Kelvysb/OpenDials/Hardware/Printing/V2/Dial/Dial-Body.stl

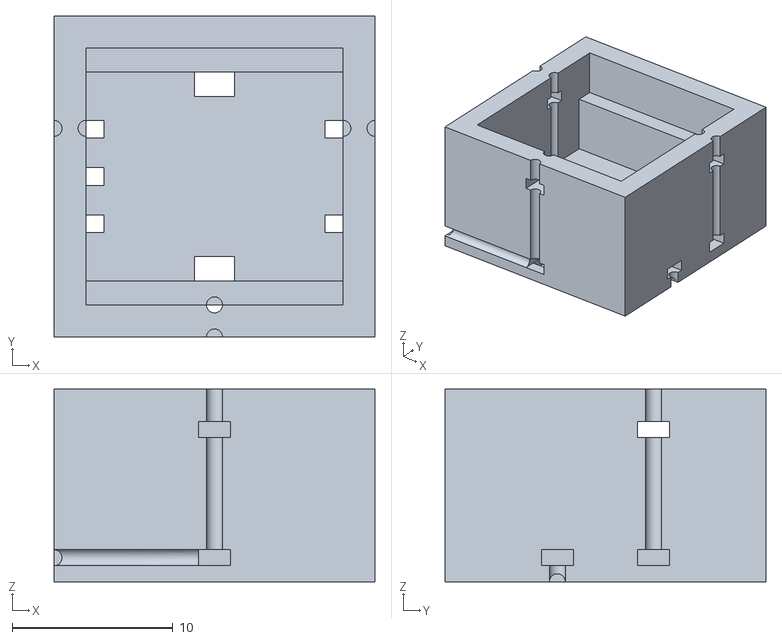
[picture p17: CAD file, 2023-11-05, an earlier design]
Hardware/Printing/V2/Dial/Dial-Body.stl
20.0 x 20.0 x 12.0
