Kelvysb/OpenDials/Hardware/Printing/V2/DPad/CE3_OpenDials_v2-DPad-Body.3mf

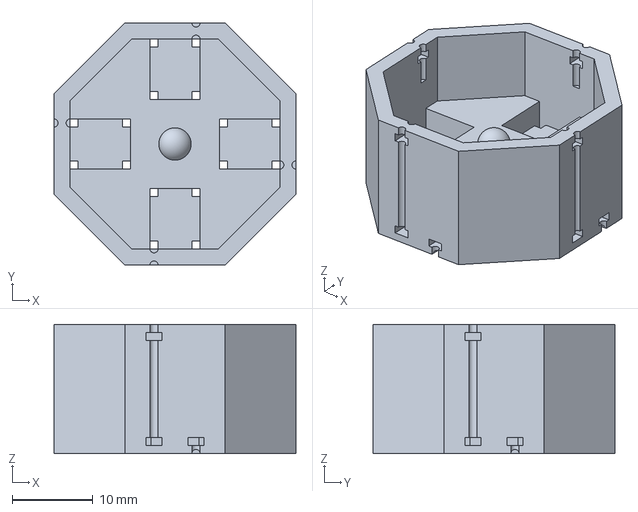
[picture p18: CAD file, 2023-10-17, an earlier design]
Hardware/Printing/V2/DPad/CE3_OpenDials_v2-DPad-Body.3mf
30.0 x 30.0 x 16.0 mm
