Kelvysb/OpenDials/Hardware/Printing/V2/Frame/Frame.stl

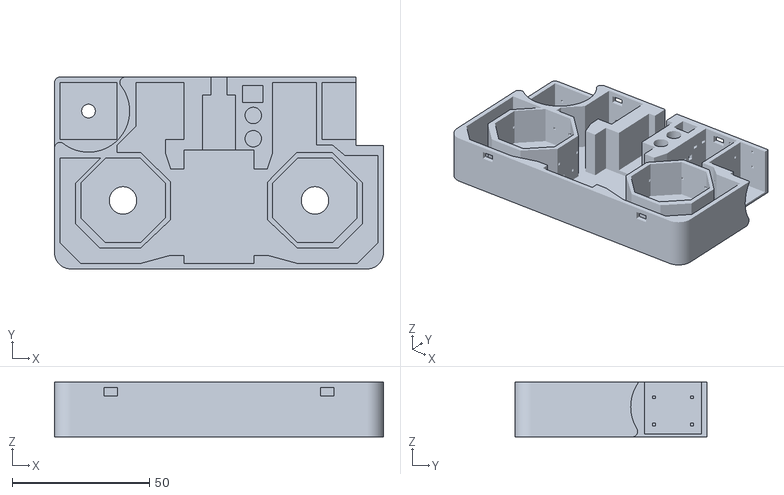
[picture p19: CAD file, 2023-11-05, an earlier design]
Hardware/Printing/V2/Frame/Frame.stl
120.0 x 70.0 x 20.0
